gvoigtlaender/EspSensorModule/ESP8266/src/CFilter.hpp

/* Copyright 2018 Georg Voigtlaender gvoigtlaender@googlemail.com */
#include <vector>

template<typename T>
class CFilter{
 public:
     explicit CFilter(unsigned int nMaxSize)
    : m_nSizeMax(nMaxSize)
    , m_nSize(0)
    , m_OutputValue()
    , m_Sum() {
    }
    T  Filter(T Value) {
      if ( m_Values.size() == 0 )
        m_Sum = Value;
      else
        m_Sum += Value;

    m_Values.push_back(Value);
    if ( m_Values.size() > m_nSizeMax ) {
      m_Sum -= m_Values[0];
      m_Values.erase(m_Values.begin());
    }
    m_nSize = m_Values.size();
    m_OutputValue = m_Sum/m_nSize;
    return m_OutputValue;
  }
  unsigned int m_nSizeMax;
  unsigned int m_nSize;
  T  m_OutputValue;
  T  m_Sum;
  std::vector<T> m_Values;
};
